rukai/rukey/rukey_flash/src/cli.rs

use clap::Parser;
use std::path::PathBuf;

#[derive(Parser, Debug)]
#[command(author, version, about, long_about = None)]
pub struct Args {
    /// Path to the rukey .kdl config file.
    /// If not specified, loads config from `config.kdl` located in the same directory as the exe/binary.
    #[arg()]
    pub path: Option<PathBuf>,
    /// Flash firmware, but overwrite existing config with 0's and do not write any config.
    /// This is only useful for development purposes, for testing invalid config.
    #[arg(long)]
    pub erase_config: bool,
}
